eminarcissus/TAS_kc/keycaps/SLA/sldprt/r1/r1_c0.SLDPRT

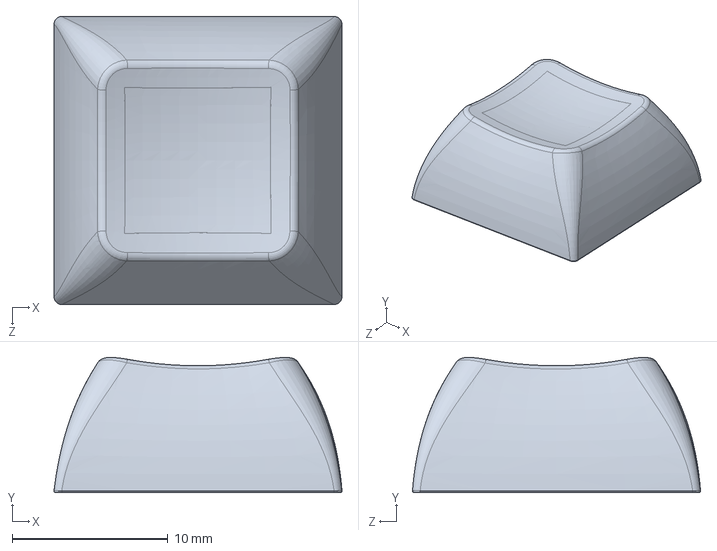
[picture p12: CAD file, 2020-01-21]
keycaps/SLA/sldprt/r1/r1_c0.SLDPRT
18.5 x 8.66 x 18.5 mm
