eminarcissus/TAS_kc/keycaps/SLA/sldprt/r0/r0_c0.SLDPRT

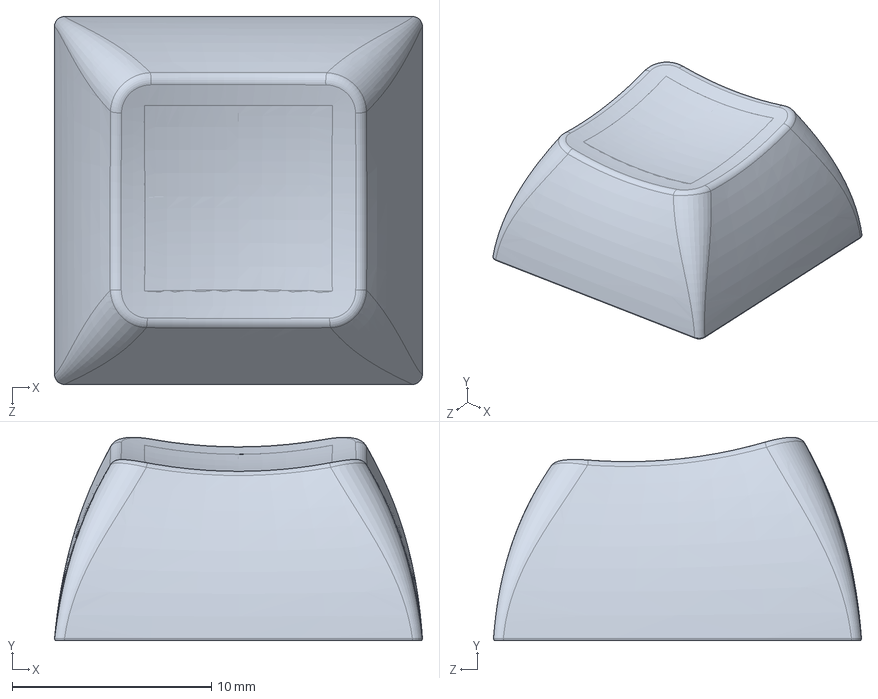
[picture p13: CAD file, 2020-01-21]
keycaps/SLA/sldprt/r0/r0_c0.SLDPRT
18.5 x 10.2 x 18.5 mm
