eminarcissus/TAS_kc/keycaps/SLA/sldprt/rn/rn_c0.SLDPRT

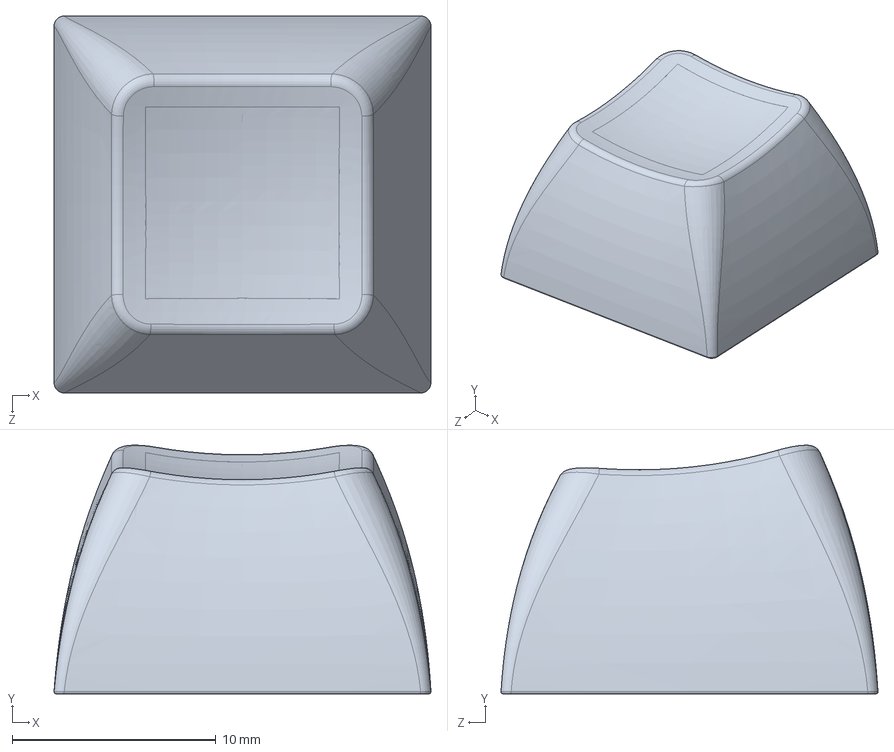
[picture p14: CAD file, 2020-01-21]
keycaps/SLA/sldprt/rn/rn_c0.SLDPRT
18.5 x 12.2 x 18.5 mm
